hgschmie/factorio-lamp-led-display/factorio-mod/lamp_led_display/stdlib/area/orientation.lua

--- Functions for working with orientations.
-- @module Area.Orientation
-- @usage local Orientation = require('stdlib.area.orientation')

local Orientation = {
    __class = 'Orientation',
    __index = require('stdlib.core'),
}
setmetatable(Orientation, Orientation)

--- north orientation
Orientation.north = defines.direction.north / 16
--- east orientation
Orientation.east = defines.direction.east / 16
--- west orientation
Orientation.west = defines.direction.west / 16
--- south orientation
Orientation.south = defines.direction.south / 16
--- northeast orientation
Orientation.northeast = defines.direction.northeast / 16
--- northwest orientation
Orientation.northwest = defines.direction.northwest / 16
--- southeast orientation
Orientation.southeast = defines.direction.southeast / 16
--- southwest orientation
Orientation.southwest = defines.direction.southwest / 16

-- 2.0 stuff

Orientation.northnortheast = defines.direction.northnortheast / 16
Orientation.northnorthwest = defines.direction.northnorthwest / 16
Orientation.eastnortheast = defines.direction.eastnortheast / 16
Orientation.eastsoutheast = defines.direction.eastsoutheast / 16
Orientation.southsoutheast = defines.direction.southsoutheast / 16
Orientation.southsouthwest = defines.direction.southsouthwest / 16
Orientation.westnorthwest = defines.direction.westnorthwest / 16
Orientation.westsouthwest = defines.direction.westsouthwest / 16

local floor = math.floor

--- Returns a 4way or 8way direction from an orientation.
---@param orientation number
---@param eight_way? boolean
---@return defines.direction
function Orientation.to_direction(orientation, eight_way)
    local ways = eight_way and 16 or 8
    local mod = eight_way and 2 or 4
    return floor(orientation * ways + 0.5) % ways * mod
end

--- Returns the opposite orientation.
---@param orientation number
---@return number orientation the opposite orientation
function Orientation.opposite(orientation)
    return (orientation + 0.5) % 1
end

--- Add two orientations together.
---@param orientation1 number
---@param orientation2 number
---@return number orientation the orientations added together
function Orientation.add(orientation1, orientation2)
    return (orientation1 + orientation2) % 1
end

return Orientation
